cprastyawan/EFALCON-FC/Firmware/F407-EFALCON4/Core/Inc/bmp2_app.h

/*
 * bmp2_app.h
 *
 *  Created on: Jun 21, 2021
 *      Author: LENOVO
 */

#ifndef INC_BMP2_APP_H_
#define INC_BMP2_APP_H_

#include <stdio.h>
#include "bmp2.h"

/***************************************************************************/

/*!                 User function prototypes
 ****************************************************************************/

/*!
 *  @brief Function for reading the sensor's registers through SPI bus.
 *
 *  @param[in] reg_addr   : Register address.
 *  @param[out] reg_data  : Pointer to the data buffer to store the read data.
 *  @param[in] length     : No of bytes to read.
 *  @param[in] intf_ptr   : Interface pointer
 *
 *  @return Status of execution
 *
 *  @retval BMP2_INTF_RET_SUCCESS -> Success.
 *  @retval != BMP2_INTF_RET_SUCCESS -> Failure.
 *
 */
BMP2_INTF_RET_TYPE bmp2_spi_read(uint8_t reg_addr, uint8_t *reg_data, uint32_t length, void *intf_ptr);

/*!
 *  @brief Function for reading the sensor's registers through I2C bus.
 *
 *  @param[in] reg_addr   : Register address.
 *  @param[out] reg_data  : Pointer to the data buffer to store the read data.
 *  @param[in] length     : No of bytes to read.
 *  @param[in] intf_ptr   : Interface pointer
 *
 *  @return Status of execution
 *
 *  @retval BMP2_INTF_RET_SUCCESS -> Success.
 *  @retval != BMP2_INTF_RET_SUCCESS -> Failure.
 *
 */
BMP2_INTF_RET_TYPE bmp2_i2c_read(uint8_t reg_addr, uint8_t *reg_data, uint32_t length, void *intf_ptr);

/*!
 *  @brief Function for writing the sensor's registers through SPI bus.
 *
 *  @param[in] reg_addr   : Register address.
 *  @param[in] reg_data   : Pointer to the data buffer whose data has to be written.
 *  @param[in] length     : No of bytes to write.
 *  @param[in] intf_ptr   : Interface pointer
 *
 *  @return Status of execution
 *
 *  @retval BMP2_INTF_RET_SUCCESS -> Success.
 *  @retval != BMP2_INTF_RET_SUCCESS -> Failure.
 *
 */
BMP2_INTF_RET_TYPE bmp2_spi_write(uint8_t reg_addr, const uint8_t *reg_data, uint32_t length, void *intf_ptr);

/*!
 *  @brief Function for writing the sensor's registers through I2C bus.
 *
 *  @param[in] reg_addr : Register address.
 *  @param[in] reg_data : Pointer to the data buffer whose value is to be written.
 *  @param[in] length   : No of bytes to write.
 *  @param[in] intf_ptr : Interface pointer
 *
 *  @return Status of execution
 *
 *  @retval BMP2_INTF_RET_SUCCESS -> Success.
 *  @retval != BMP2_INTF_RET_SUCCESS -> Failure.
 *
 */
BMP2_INTF_RET_TYPE bmp2_i2c_write(uint8_t reg_addr, const uint8_t *reg_data, uint32_t length, void *intf_ptr);

/*!
 *  @brief This function provides the delay for required time (Microsecond) as per the input provided in some of the
 *  APIs.
 *
 *  @param[in] period_us  : The required wait time in microsecond.
 *  @param[in] intf_ptr   : Interface pointer
 *
 *  @return void.
 */
void bmp2_delay_us(uint32_t period_us, void *intf_ptr);

/*!
 *  @brief This function is to select the interface between SPI and I2C.
 *
 *  @param[in] dev    : Structure instance of bmp2_dev
 *  @param[in] intf   : Interface selection parameter
 *                          For I2C : BMP2_I2C_INTF
 *                          For SPI : BMP2_SPI_INTF
 *
 *  @return Status of execution
 *  @retval 0 -> Success
 *  @retval < 0 -> Failure
 */
int8_t bmp2_interface_selection(struct bmp2_dev *dev, uint8_t intf);

/*!
 *  @brief This API is used to print the execution status.
 *
 *  @param[in] api_name : Name of the API whose execution status has to be printed.
 *  @param[in] rslt     : Error code returned by the API whose execution status has to be printed.
 *
 *  @return void.
 */
void bmp2_error_codes_print_result(const char api_name[], int8_t rslt);

#endif /* INC_BMP2_APP_H_ */
